devicefuture/digicron/firmware/fs.cpp

#include "fs.h"
#include "datatypes.h"

auto openFileHandles = dataTypes::List<fs::FileHandle>();

fs::FileHandle::FileHandle(proc::Process* process) : fs::FileHandle::FileHandle() {
    ownerProcess = process;
}

fs::FileHandle::FileHandle(String path, FileMode mode) {
    bool isAlreadyOpen = isFileOpen(path);
    char pathCharArray[path.length() + 1];

    _path = path;
    _mode = mode;
    _isOpen = true;
    _errorOnOpen = false;
    _alreadyOpen = false;

    path.toCharArray(pathCharArray, sizeof(pathCharArray));

    openFileHandles.push(this);

    if (isAlreadyOpen) {
        _errorOnOpen = true;
        _alreadyOpen = true;
        close();
        return;
    }

    if (path == "" || !_openFile(pathCharArray)) {
        _errorOnOpen = true;
        close();
        return;
    }
}

fs::FileHandle::FileHandle(proc::Process* process, String path, FileMode mode) : fs::FileHandle::FileHandle(path, mode) {
    ownerProcess = process;
}

fs::FileHandle::~FileHandle() {
    close();
}

String fs::FileHandle::readString() {
    String data = "";

    while (isAvailable()) {
        char c = read();

        if (c == '\0') {
            break;
        }

        data += c;
    }

    return data;
}

char* fs::FileHandle::readBuffer(unsigned int* sizePtr) {
    char* buffer = (char*)malloc(0);
    unsigned int size = 0;

    while (isAvailable()) {
        char c = read();

        buffer = (char*)realloc(buffer, size + 1);
        buffer[size++] = c;
    }

    buffer = (char*)realloc(buffer, size + 1);
    buffer[size++] = '\0';

    if (sizePtr) {
        *sizePtr = size;
    }

    return buffer;
}

void fs::FileHandle::write(String string) {
    for (unsigned int i = 0; i < string.length(); i++) {
        write(string[i]);
        i++;
    }
}

void fs::FileHandle::seek(int position, fs::SeekOrigin origin) {
    if (!isAvailable()) {
        return;
    }

    switch (origin) {
        case SeekOrigin::START:
        default:
            break;

        case SeekOrigin::CURRENT:
            position += tell();
            break;

        case SeekOrigin::END:
            position += getSize();
            break;
    }

    _seekFile(position);
}

void fs::FileHandle::start() {
    seek(0);
}

void fs::FileHandle::close() {
    if (!_isOpen) {
        return;
    }

    _isOpen = false;

    int handleIndex = openFileHandles.indexOf(this);

    if (handleIndex >= 0) {
        openFileHandles.remove(handleIndex);
    }

    if (_alreadyOpen) {
        Serial.print("Unable to open file at path because it is already open elsewhere: ");
        Serial.println(_path);
        return;
    }

    if (_errorOnOpen) {
        Serial.print("Unable to open file at path: ");
        Serial.println(_path);
        return;
    }

    _closeFile();
}

fs::DirectoryListing::~DirectoryListing() {
    _entries.emptyAndDelete();
}

String fs::DirectoryListing::next() {
    String* entry = _entries.next();

    if (entry) {
        return *entry;
    } else {
        return "";
    }
}

fs::FileHandle* fs::open(proc::Process* process, String path, fs::FileMode mode) {
    auto fileHandle = new FileHandle(process, path, mode);

    if (!fileHandle->isOpen()) {
        return nullptr;
    }

    return fileHandle;
}

fs::FileHandle* fs::open(String path, fs::FileMode mode) {
    return open(nullptr, path, mode);
}

bool fs::isFileOpen(String path) {
    openFileHandles.start();

    while (auto fileHandle = openFileHandles.next()) {
        if (fileHandle->getPath() == path) {
            return true;
        }
    }

    return false;
}
