devicefuture/digicron/firmware/ui/menus.h

#ifndef UI_MENUS_H_
#define UI_MENUS_H_

#include "../ui.h"
#include "../timing.h"

namespace ui {
    class Menu : public Screen {
        public:
            using Screen::Screen;

            dataTypes::List<String> items;

            Menu(dataTypes::List<String> menuItems) : Screen() {
                items = menuItems;
            }

            ~Menu();

            void clearItems();
            void addItem(String item) {items.push(new String(item));}
            unsigned int getCurrentIndex() {return _currentIndex;}
            void setCurrentIndex(unsigned int index) {_currentIndex = index;}
            void setIsLoading(bool isLoading) {_isLoading = isLoading;}

            virtual void open(bool urgent = false) override;

            void update() override;
            void _handleEvent(Event event) override;

        protected:
            unsigned int _currentIndex = 0;
            unsigned int _scrollPosition = 0;
            bool _isLoading = false;
    };

    class ContextualMenu : public Menu {
        public:
            using Menu::Menu;

            ContextualMenu(String title) : Menu() {
                setTitle(title);
            }

            ContextualMenu(proc::Process* process, String title) : Menu(process) {
                setTitle(title);
            }

            String getTitle() {return _title;}
            void setTitle(String title) {_title = title;}
            bool getSelectionBlinking() {return _blinkSelection;}

            void setSelectionBlinking(bool blinkSelection) {
                _blinkSelection = blinkSelection;
                _blinkStartTime = timing::getCurrentTick();
            }

            void open(bool urgent = false) override;
            void update() override;
            void _handleEvent(Event event) override;

        protected:
            String _title = "";
            bool _blinkSelection = false;
            unsigned int _blinkStartTime = 0;
    };

    class ConfirmationMenu : public ContextualMenu {
        public:
            ConfirmationMenu();
            ConfirmationMenu(proc::Process* process);
            ConfirmationMenu(String title, bool swapYesNo = false);
            ConfirmationMenu(proc::Process* process, String title, bool swapYesNo = false);

            bool yesSelected();

            void update() override;
            void _handleEvent(Event event) override;
    };

    extern String* yesOption;
    extern String* noOption;
    extern Icon* menuSelectionIcon;
    extern Icon* menuScrollableIcon;
    extern Icon* menuLoadingIcon;
}

#include "textinputs.h"

#endif
